trlafleur/WaterMeter-MS-3.0i-RFM95/Doc/Photos/IMG_5081.jpeg

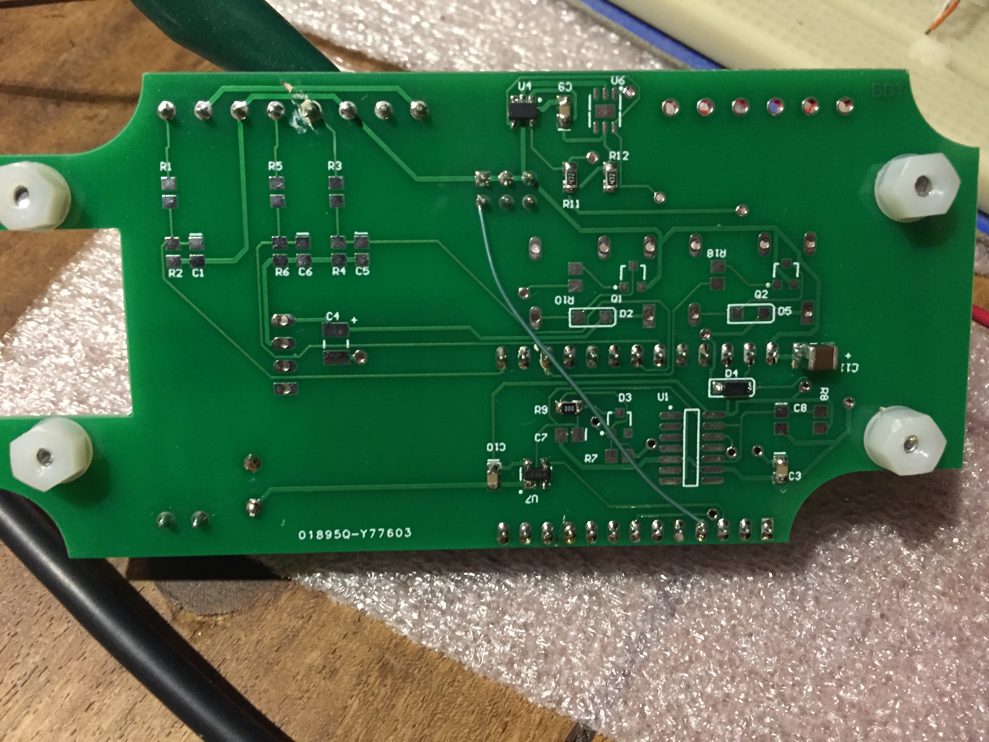
Doc/Photos/IMG_5081.jpeg
